Acmex2564/Z31-ECU-Breakout/IMG_20220412_1746245.jpg

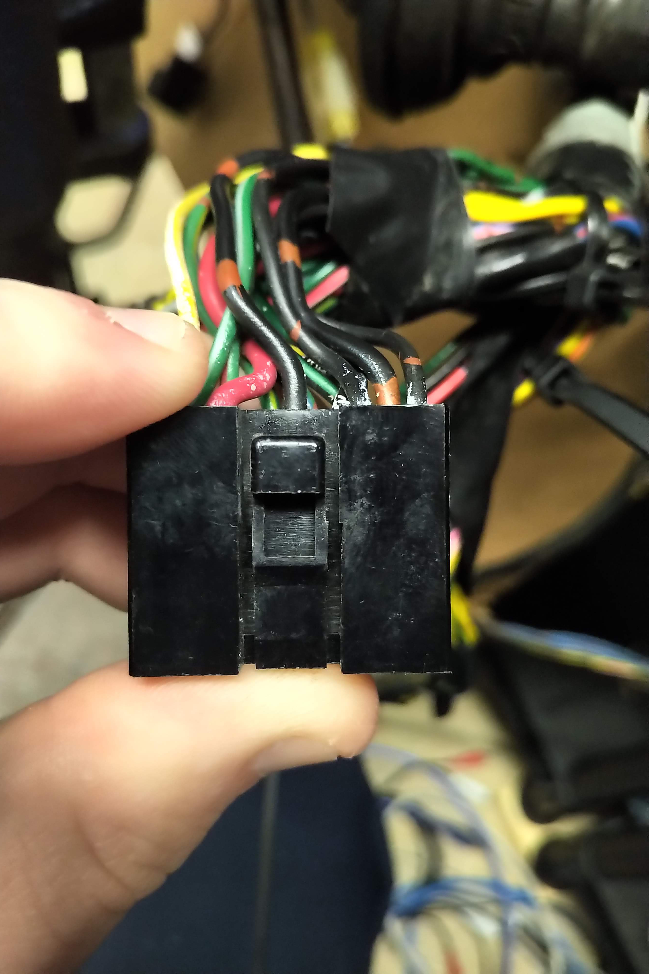
IMG_20220412_1746245.jpg
