Acmex2564/Z31-ECU-Breakout/IMG_20220412_1749372.jpg

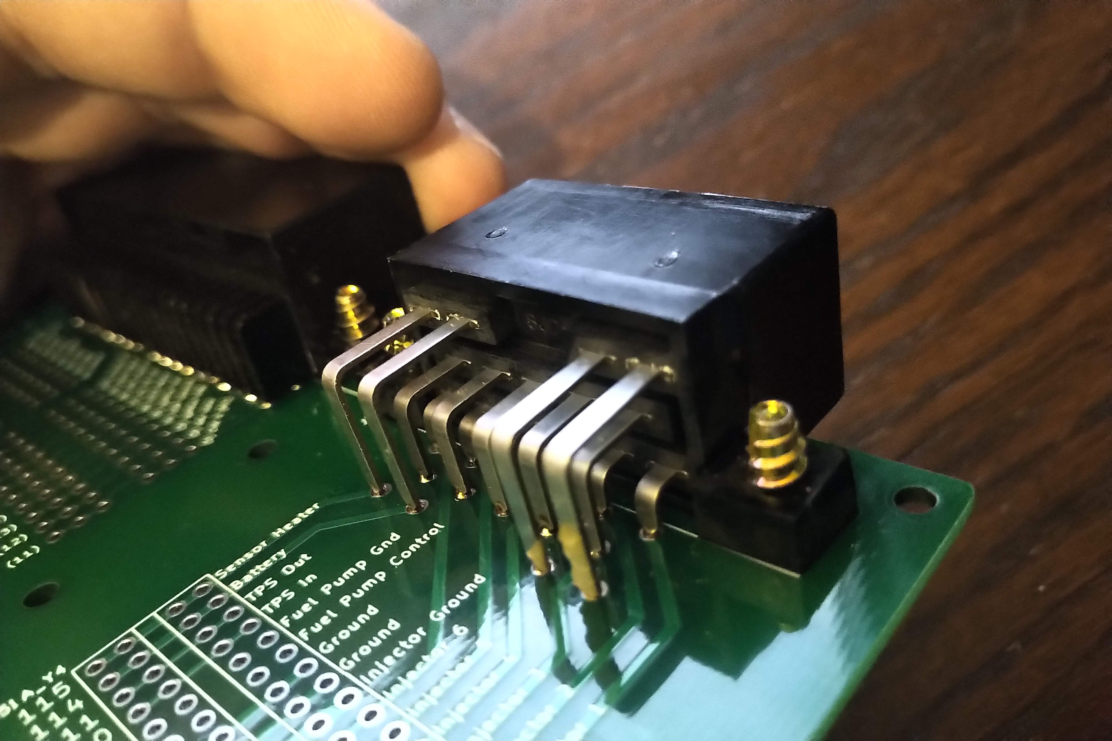
IMG_20220412_1749372.jpg
